chdao/PanicPedal/esp32/receiver/infrastructure/DebugMonitor.h

#ifndef DEBUG_MONITOR_H
#define DEBUG_MONITOR_H

#include <stdint.h>
#include <stdbool.h>
#include <stdarg.h>
#include "../infrastructure/EspNowTransport.h"

#define MAX_BUFFERED_MESSAGES 50  // Limit buffer size to prevent memory issues

typedef struct {
  ReceiverEspNowTransport* transport;
  uint8_t mac[6];
  bool paired;
  bool espNowInitialized;
  unsigned long bootTime;
  
  // Message buffer for messages sent before debug monitor discovery
  char messageBuffer[MAX_BUFFERED_MESSAGES][200];
  int bufferCount;
  int bufferIndex;  // For circular buffer
} DebugMonitor;

void debugMonitor_init(DebugMonitor* monitor, ReceiverEspNowTransport* transport, unsigned long bootTime);
void debugMonitor_load(DebugMonitor* monitor);
void debugMonitor_save(DebugMonitor* monitor);
void debugMonitor_print(DebugMonitor* monitor, const char* format, ...);
void debugMonitor_handleDiscoveryRequest(DebugMonitor* monitor, const uint8_t* senderMAC, uint8_t channel);
void debugMonitor_sendBufferedMessages(DebugMonitor* monitor);  // Public function to send buffered messages

#endif // DEBUG_MONITOR_H
