chdao/PanicPedal/esp32/shared/transmitter/TransmitterConstants.h

#ifndef TRANSMITTER_CONSTANTS_H
#define TRANSMITTER_CONSTANTS_H

// ============================================================================
// Constants that must be defined BEFORE config.h is included
// ============================================================================

// Pedal mode constants
#define PEDAL_MODE_AUTO -1
#define PEDAL_MODE_DUAL 0
#define PEDAL_MODE_SINGLE 1

#endif // TRANSMITTER_CONSTANTS_H
